TanLaura/TECHIN514-final/Enclosure/Display_Enclosure/display_bottom.stl

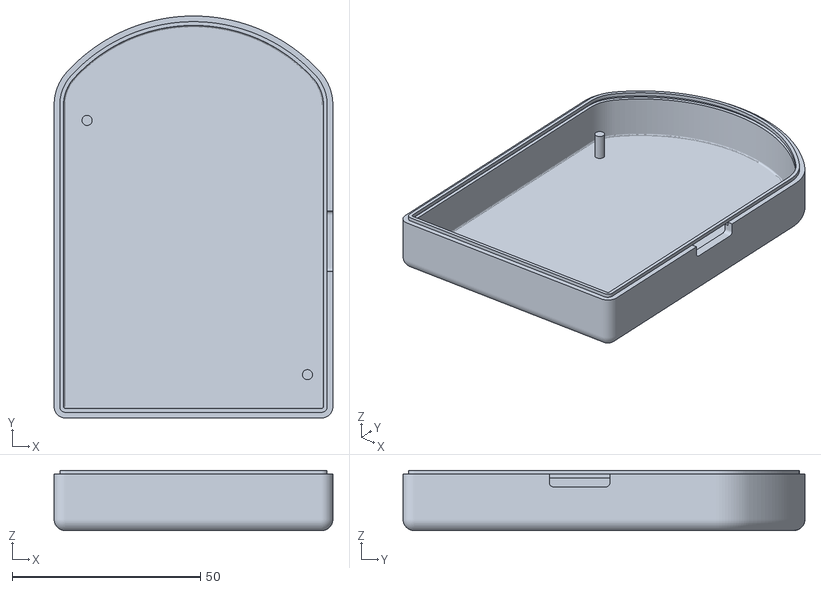
[picture p19: CAD file, 2025-03-11]
Enclosure/Display_Enclosure/display_bottom.stl
74.0 x 106.7 x 16.0
