TanLaura/TECHIN514-final/Enclosure/Sensor_Enclosure/Sensor_enclosure v5.step

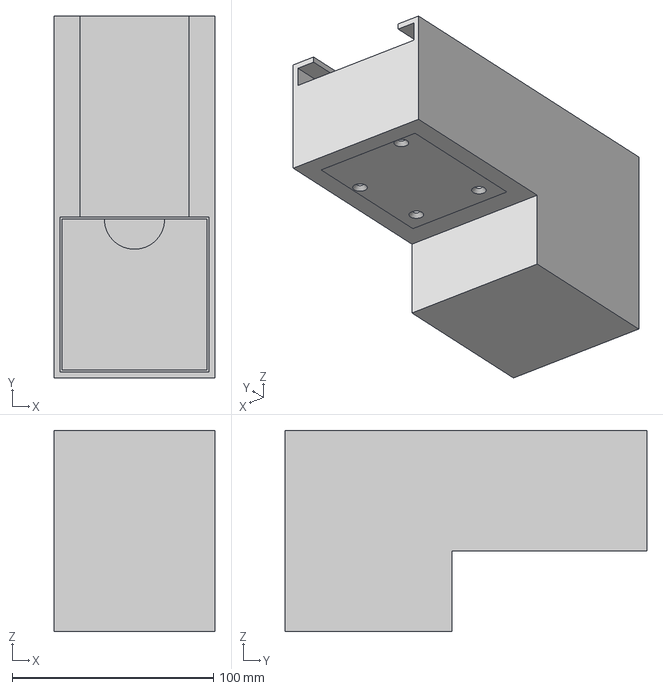
[picture p20: CAD file, 2025-03-11]
Enclosure/Sensor_Enclosure/Sensor_enclosure v5.step
80.0 x 180.0 x 100.0 mm
514_final_sensor_pcb_PCB
Drawer
